hamspot/hs736usb/Hardware/Artwork/v2/render_bottom.png

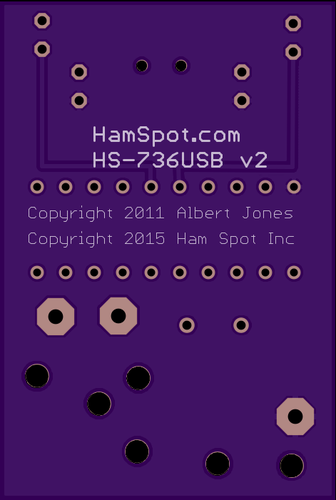
Hardware/Artwork/v2/render_bottom.png
