hamspot/hs736usb/Hardware/Artwork/v2/render_top.png

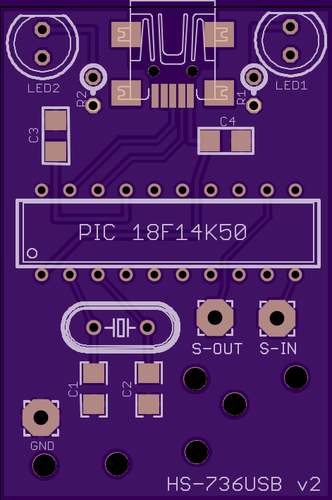
Hardware/Artwork/v2/render_top.png
