hamspot/hs736usb/Hardware/Cabinet/v2.1/HS-736RUSB-Enclosure-Ortho.png

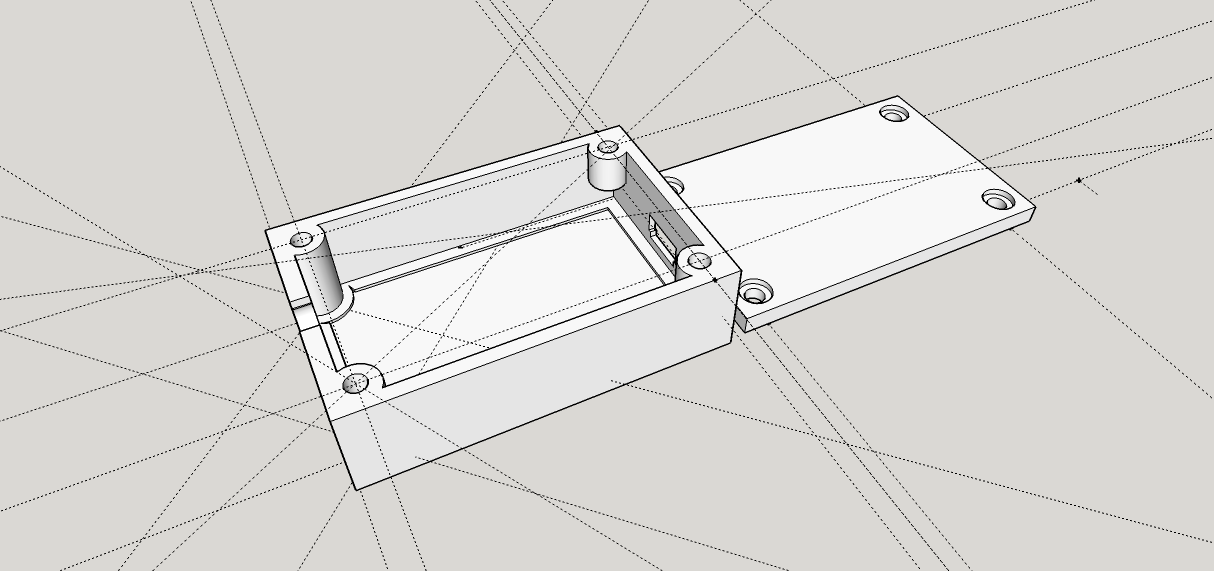
Hardware/Cabinet/v2.1/HS-736RUSB-Enclosure-Ortho.png
