hamspot/hs736usb/Manual/figures/fig-power-rear.png

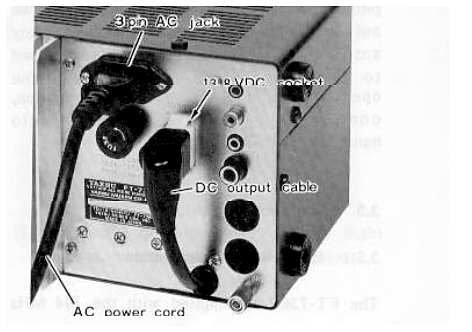
Manual/figures/fig-power-rear.png
